Trefex/arduino-airquality/aq6s/outputs/2014-02-09 21.30.06.jpg

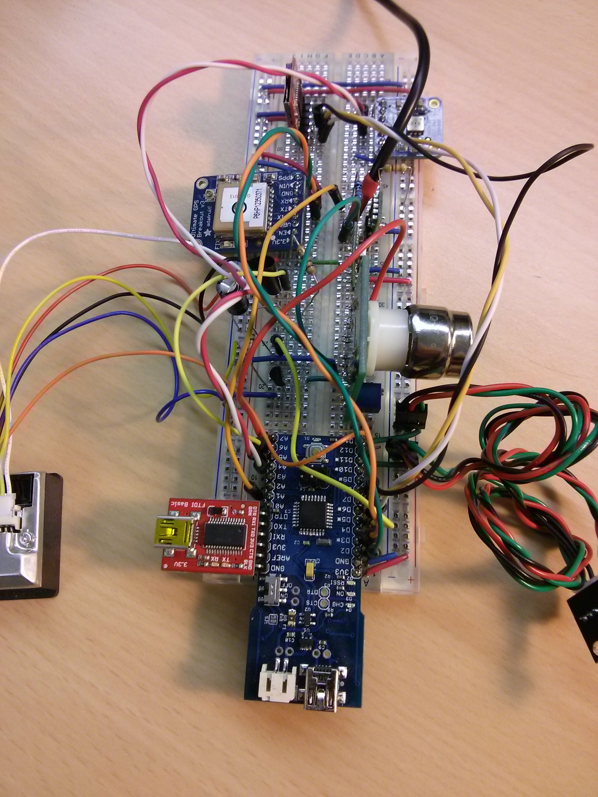
aq6s/outputs/2014-02-09 21.30.06.jpg
