Trefex/arduino-airquality/Module_COSensor/outputs/First_70m_cooking.png

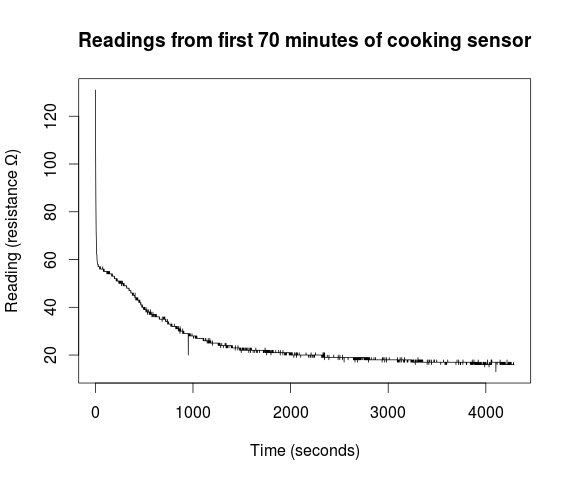
Module_COSensor/outputs/First_70m_cooking.png
