Trefex/arduino-airquality/Module_COSensor/outputs/Rplot01.png

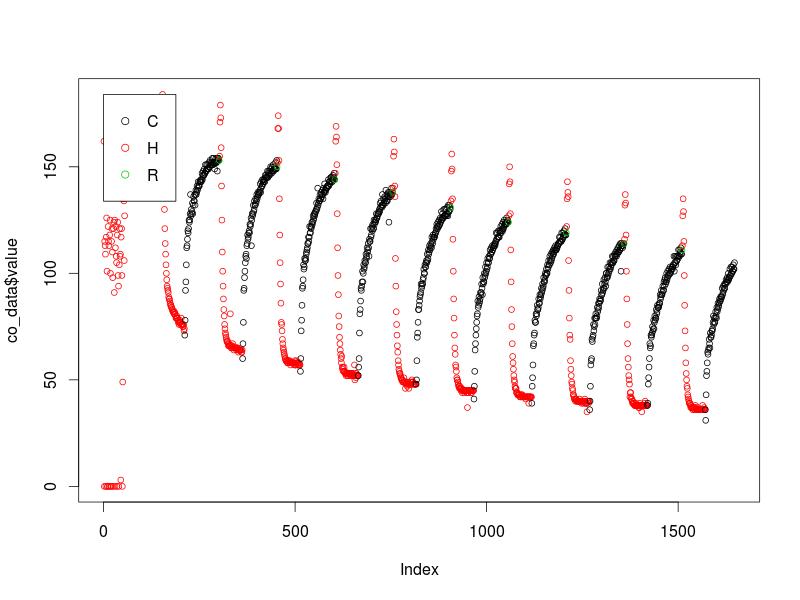
Module_COSensor/outputs/Rplot01.png
