Trefex/arduino-airquality/Module_COSensor/outputs/Rplot.png

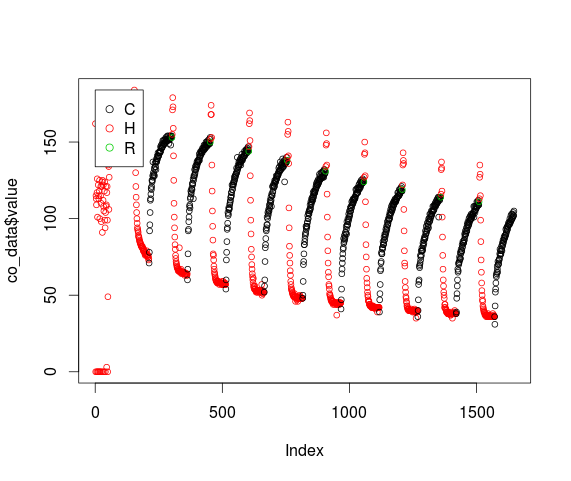
Module_COSensor/outputs/Rplot.png
