Trefex/arduino-airquality/Module_COSensor/outputs/unstable_readings.png

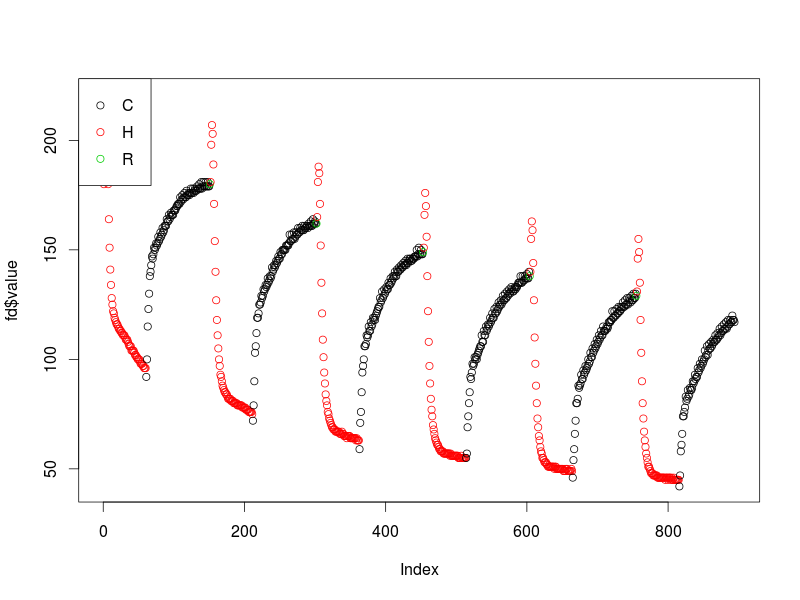
Module_COSensor/outputs/unstable_readings.png
