Trefex/arduino-airquality/schematics/Eagle/Screen Shot 2014-04-05 at 9.56.28 PM.png

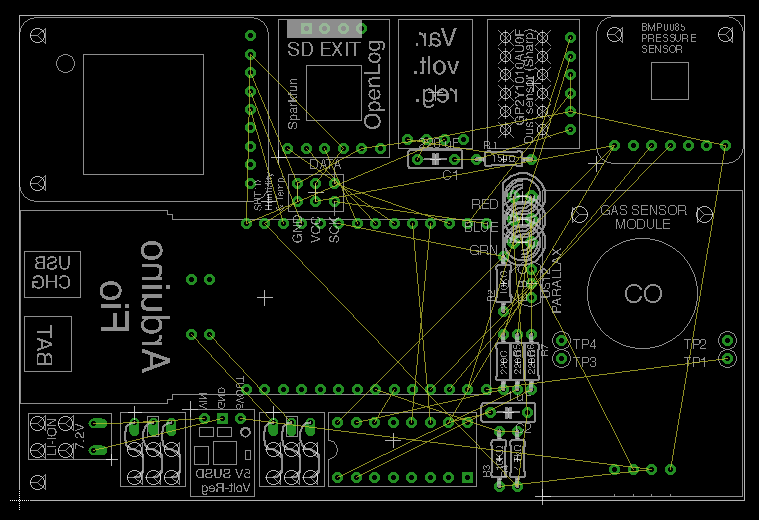
schematics/Eagle/Screen Shot 2014-04-05 at 9.56.28 PM.png
