Trefex/arduino-airquality/Module_Dust-GPS-OpenLog/assembly/_Blog Images/gps_sd_zoom.JPG

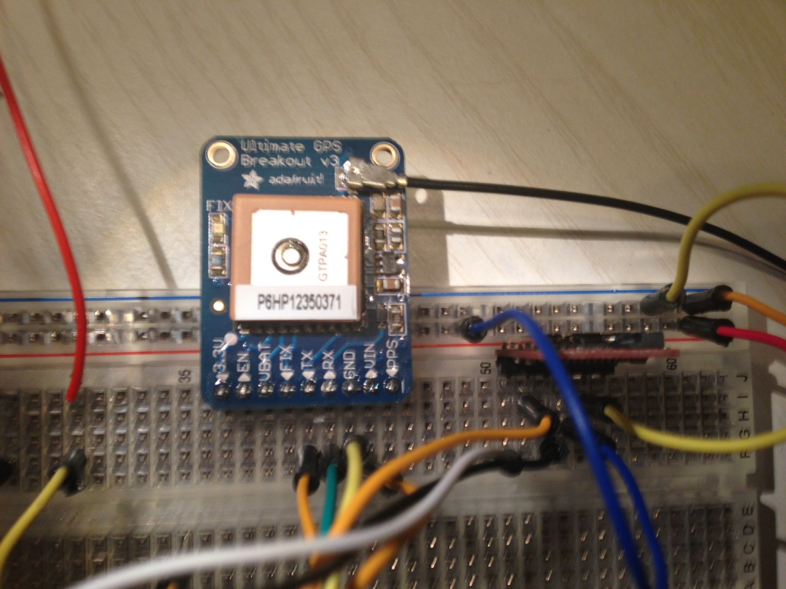
Module_Dust-GPS-OpenLog/assembly/_Blog Images/gps_sd_zoom.JPG
