Trefex/arduino-airquality/Module_Dust-GPS-OpenLog/assembly/_Blog Images/overall_setup.JPG

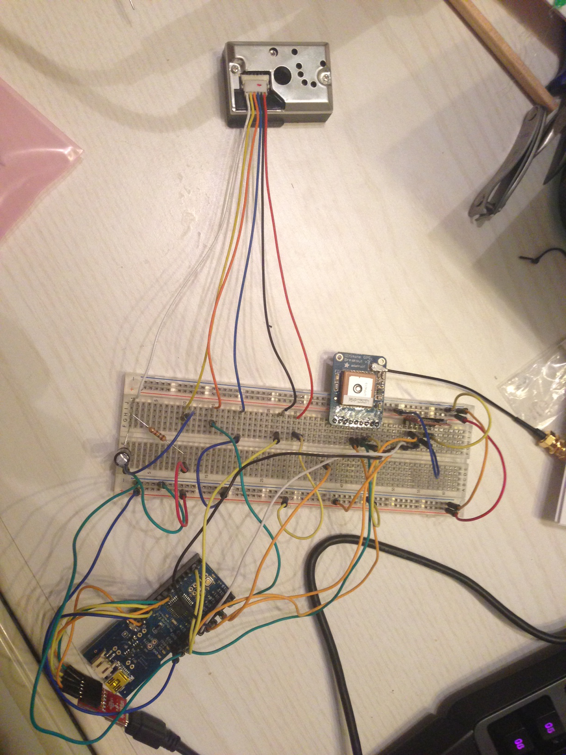
Module_Dust-GPS-OpenLog/assembly/_Blog Images/overall_setup.JPG
