Trefex/arduino-airquality/Module_Dust-Sensor/assembly/_BlogImages/Arduino_Dust3.JPG

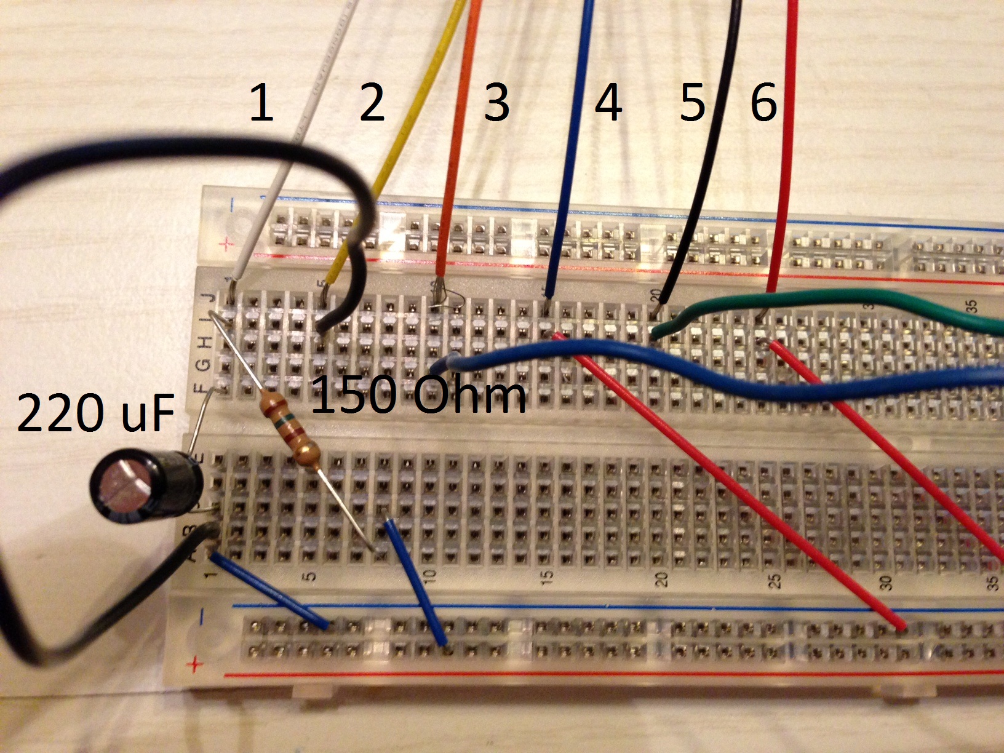
Module_Dust-Sensor/assembly/_BlogImages/Arduino_Dust3.JPG
