Trefex/arduino-airquality/Module_Dust-Sensor/assembly/_BlogImages/ArduinoUno_Dust4.JPG

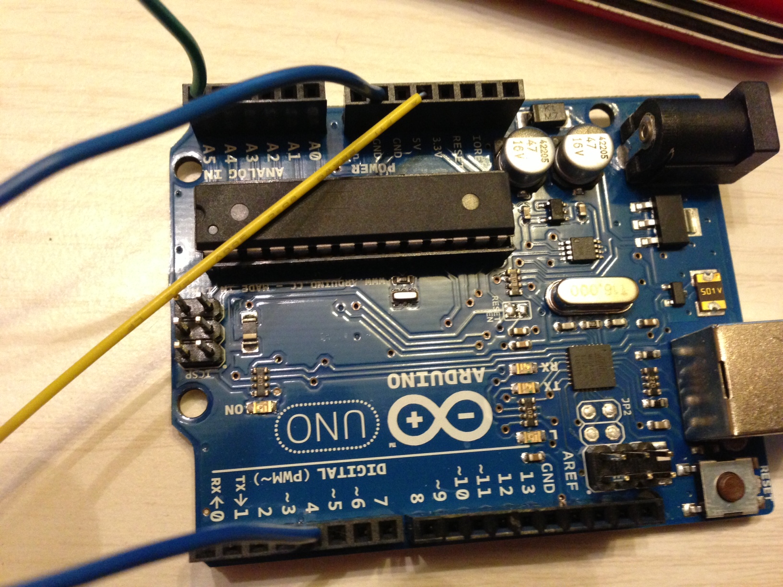
Module_Dust-Sensor/assembly/_BlogImages/ArduinoUno_Dust4.JPG
