Trefex/arduino-airquality/Module_Dust-Sensor/assembly/_BlogImages/Sharp_Sampling.PNG

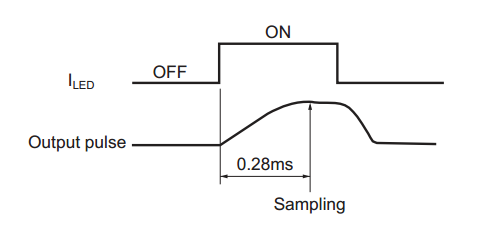
Module_Dust-Sensor/assembly/_BlogImages/Sharp_Sampling.PNG
