Trefex/arduino-airquality/Module_Dust-Sensor/assembly/_BlogImages/SharpDensitycurve.PNG

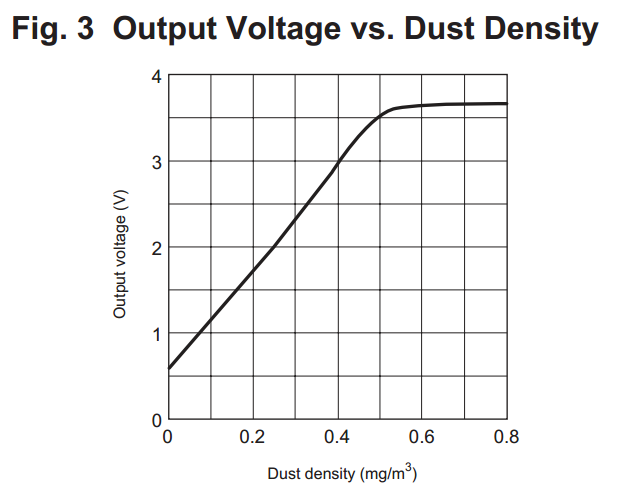
Module_Dust-Sensor/assembly/_BlogImages/SharpDensitycurve.PNG
