Trefex/arduino-airquality/Module_Dust-Sensor/assembly/_BlogImages/sharpFromDoc.png

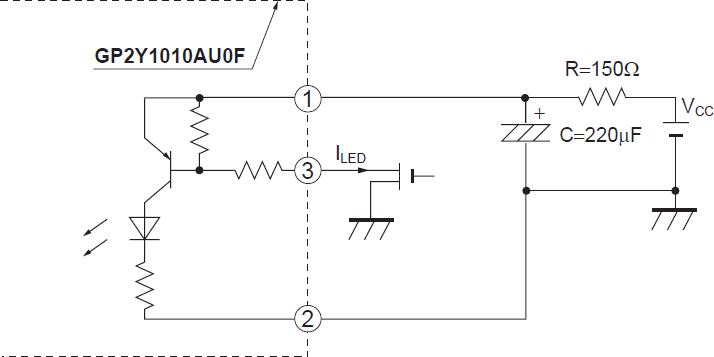
Module_Dust-Sensor/assembly/_BlogImages/sharpFromDoc.png
