Trefex/arduino-airquality/Module_Dust-Sensor/assembly/Arduino_Fio_Sketch_Fritzing_schem.jpg

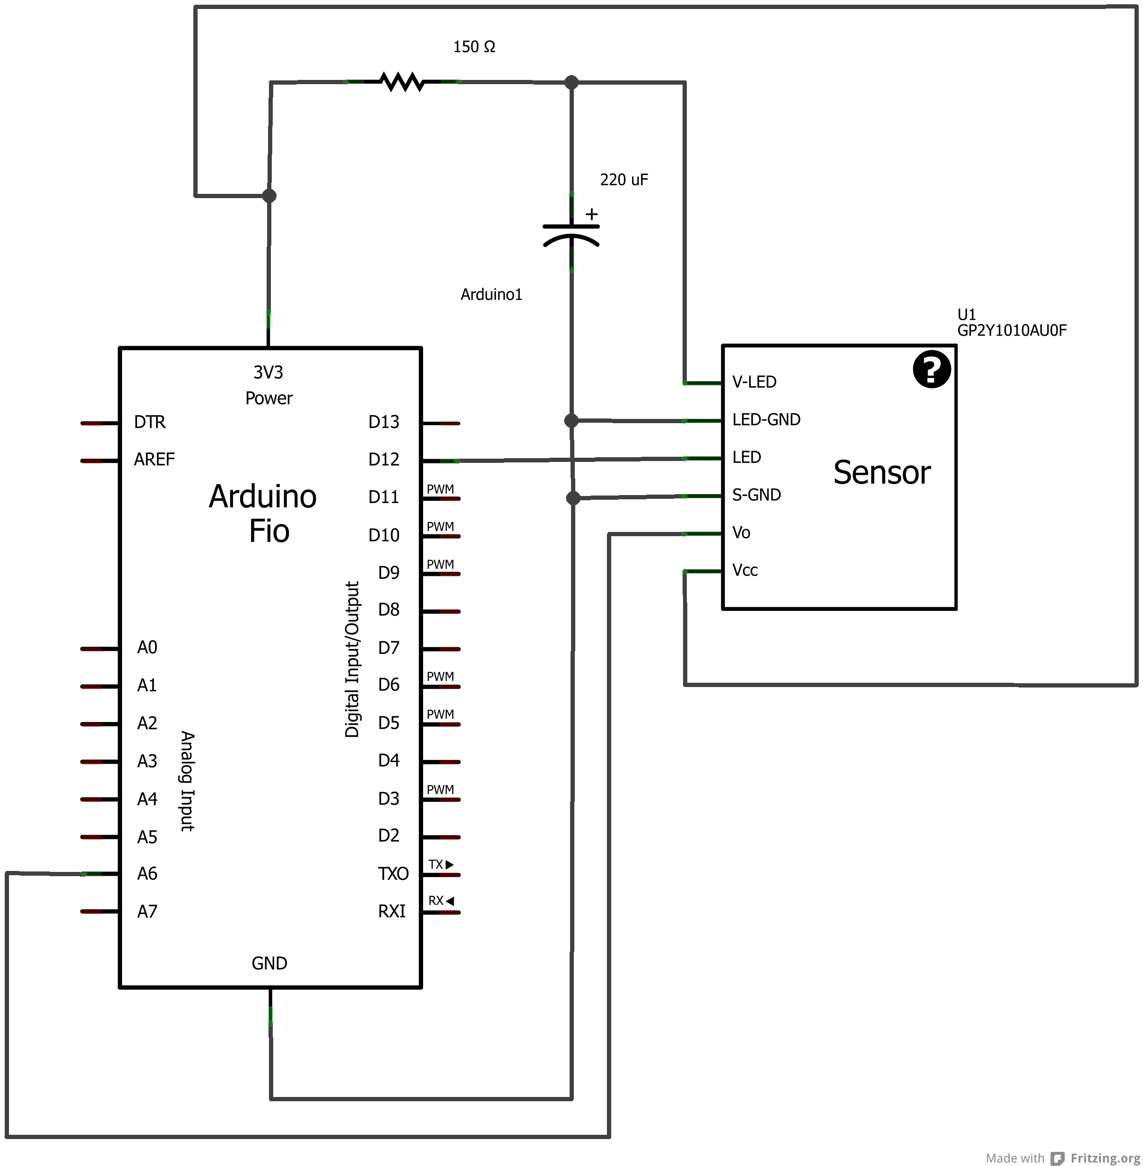
Module_Dust-Sensor/assembly/Arduino_Fio_Sketch_Fritzing_schem.jpg
