Trefex/arduino-airquality/OpenLogSerialTest/openlog_breadboard.jpg

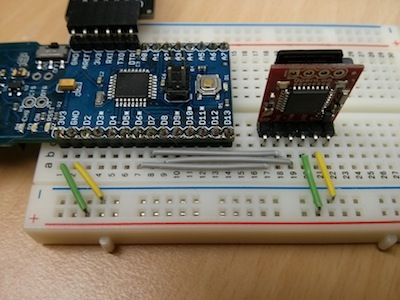
OpenLogSerialTest/openlog_breadboard.jpg
