Trefex/arduino-airquality/schematics/Fritzing/pcb/aq6s_etch_silk_bottom.pdf

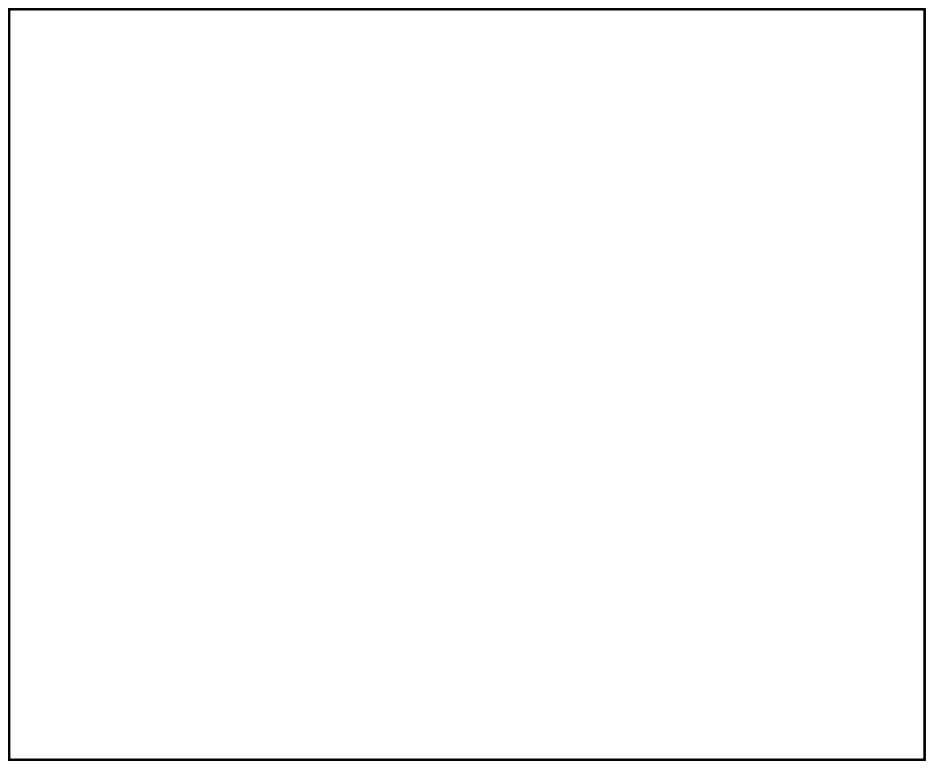
[picture p37: page 1]
