Trefex/arduino-airquality/schematics/Fritzing/pcb/aq6s_etch_silk_bottom_mirror.pdf

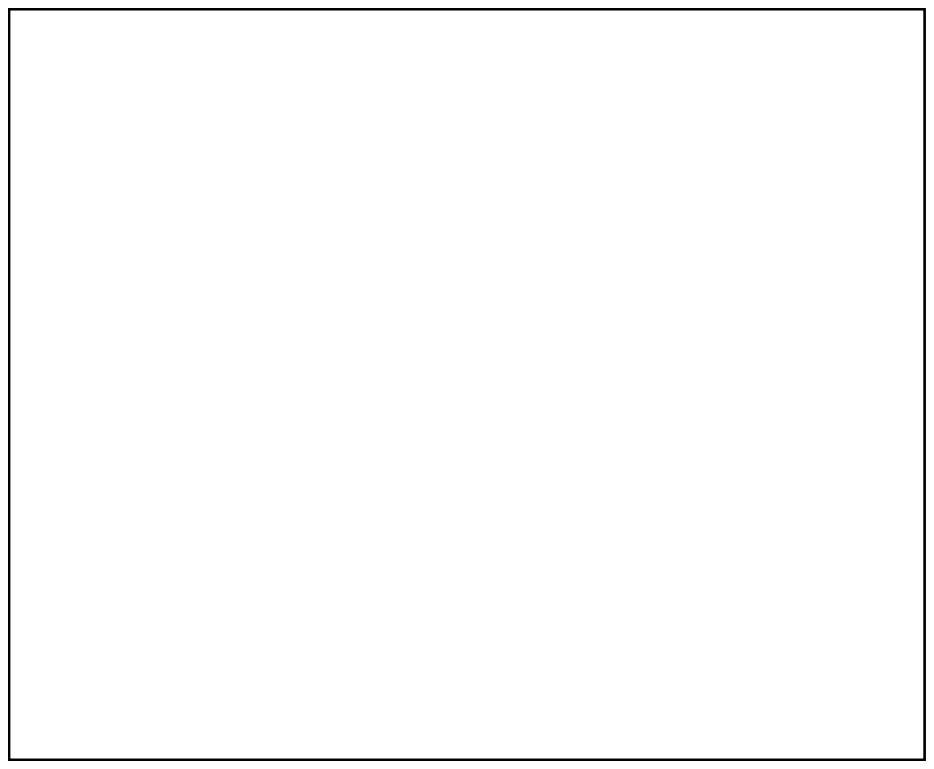
[picture p38: page 1]
