Trefex/arduino-airquality/schematics/Fritzing/pcb/aq6s_etch_silk_top.pdf

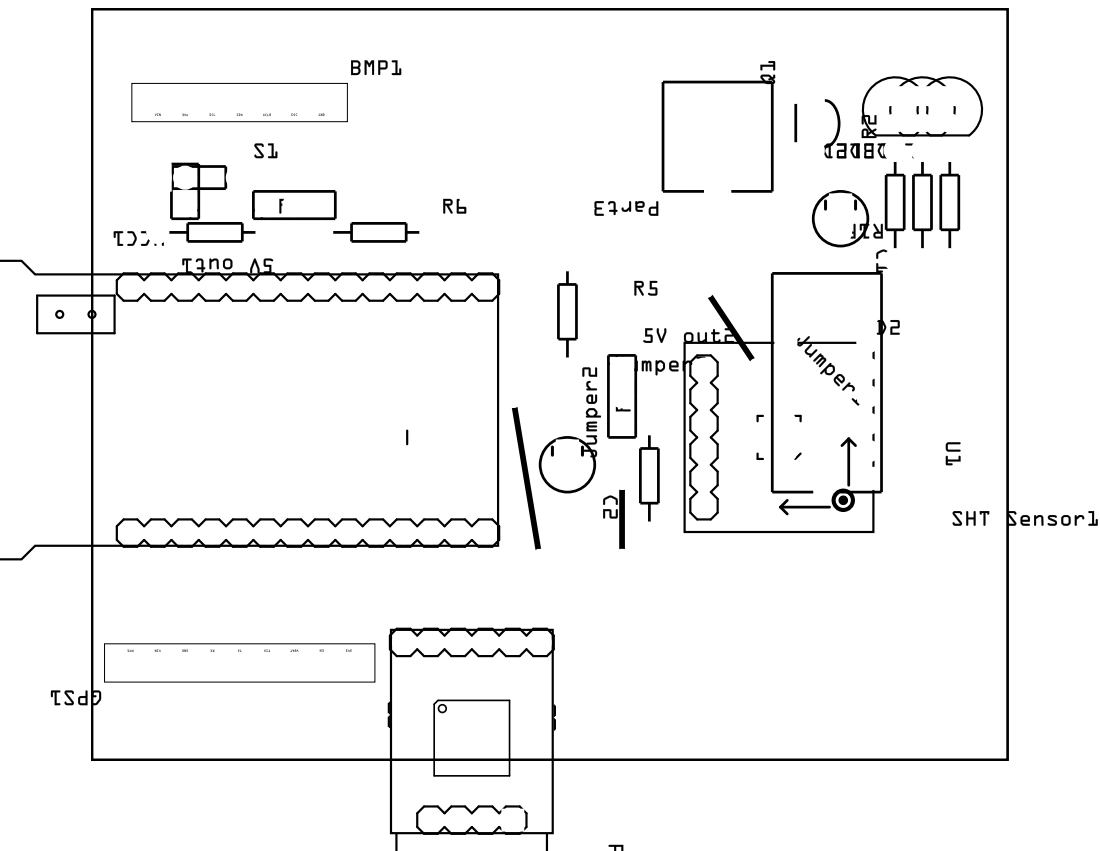
[picture p39: page 1]
