Trefex/arduino-airquality/schematics/Fritzing/pcb/aq6s_etch_silk_top_mirror.pdf

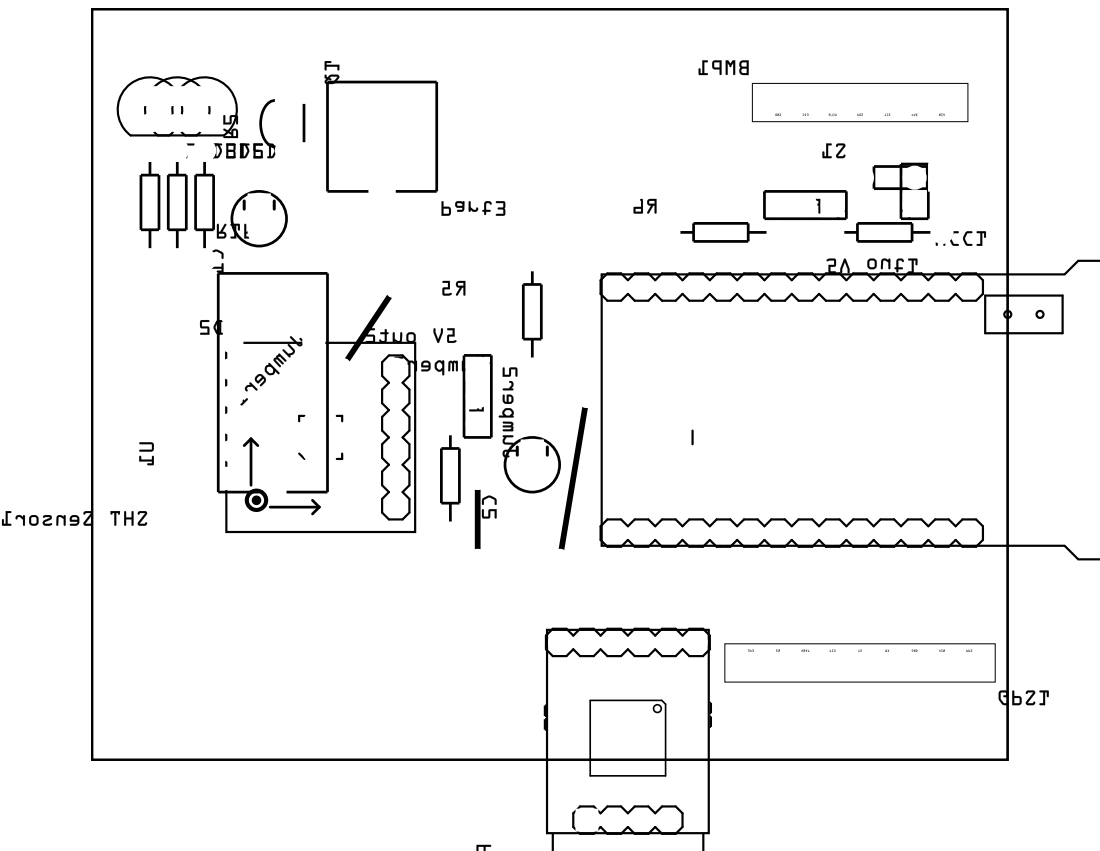
[picture p40: page 1]
